myriadrf/STREAM/hardware/STREAM/v2/v2r1/KiCAD/Board power supply 1.sch

## KiCad design hardware/STREAM/v2/v2r1/KiCAD/Board power supply 1.sch (2015-03-17)

Schematic: Board power supply 1.sch

Parts:
C140, C155: 10UF_1206; SMD1206; Manufacturer Part Number CC1206ZKY5V7BB106
C141, C156: 22NF_0402; SMD0402; Manufacturer Part Number CC0402KRX7R9BB103
C142, C157: 2.2NF_0402; SMD0402; Manufacturer Part Number CL05B222KB5NNNC
C143, C160: 22PF_0402; SMD0402; Manufacturer Part Number CC0402JRNPO9BN220
C144, C161: 0.33UF_0603; SMD0603; Manufacturer Part Number MCCA000526
C145, C162: 22UF_0805; SMD0805; Manufacturer Part Number C2012X5R0J226M125AC
C151: 1UF_0402; C_SM0402; Manufacturer Part Number CC0402ZRY5V5BB105
C152, C158, C163: 10UF_0805; C_SM0805; Manufacturer Part Number C2012JB0J106K125AB
C154: 100NF_0402; C_SM0402; Manufacturer Part Number C0402C104K8PACTU
C164: 220UF_AL_CAP; 6.3mm_Al_cap; Manufacturer Part Number UCD1C221MCL1GS
C166: 10UF_0805; C_SM0402; Manufacturer Part Number C2012JB0J106K125AB
C176, C178: 2.2UF_0603; C_SM0603; Manufacturer Part Number CC0603ZRY5V6BB225
C181: 47UF_1206; C_SM1206; Manufacturer Part Number GRM31CR60J476ME19L
D1, D10: 20BQ030; SMB; Manufacturer Part Number VS-20BQ030TRPBF
D2, D12: TS4148; SM0805; Manufacturer Part Number TS4148 RY
IC16: TPS51100DGQ; 10MSOP; Manufacturer Part Number TPS51100DGQ
IC18: MIC37122Y_ADJ; SOIC8; Manufacturer Part Number MIC37122YM TR
IC24: NCP59151-ADJ; D2PAK-5; Manufacturer Part Number NCP59151DS50R4G
J18: PWR_JACK__FC681495; PWR_JACK_TH; Manufacturer Part Number FC681495
L2, L3: 22UH_XAL60XX_SERIES; XAL60xx series; Manufacturer Part Number XAL6060-223MEB
LD7, LD8: LED_0603_GREEN; LD_0603; Manufacturer Part Number HSMG-C190
R5, R156: 1K_0402; R_SM0402; Manufacturer Part Number RMCF0402FT1K00
R49, R130: 15K8_0402; SMD0402; Manufacturer Part Number CRCW040215K8FKED
R50, R131: 28K_0402; SMD0402; Manufacturer Part Number RC0402FR-0728KL
R51: 24K9_0402; SMD0402; Manufacturer Part Number RC1005F2492CS
R52, R144: 5K49_0402; SMD0402; Manufacturer Part Number RC0402FR-075K49L
R70: 2K32_0402; R_SM0402; Manufacturer Part Number RMCF0402FT2K32
R113: 0R_0402; R_SM0402; Manufacturer Part Number RC0402JR-070RL
R132: 22K1_0402; SMD0402; Manufacturer Part Number RC0402FR-0722K1L
R141, R142: 10K_0402; R_SM0402; Manufacturer Part Number RC0402FR-0710KL
R145, R160: 0R_0805; SM0805; Manufacturer Part Number ERJ-6GEY0R00V
R157: 470R_0402; R_SM0402; Manufacturer Part Number ERA-2AED471X
R158: 3K_0402; R_SM0402; Manufacturer Part Number CRCW04023K00FKED
R159: 750R_0402; R_SM0402; Manufacturer Part Number CRCW0402750RFKED
SW5: SW_ON-OFF; Switch_On_Off; Manufacturer Part Number L102021ML04Q
U3, U7: SC4524; SOIC-8; Manufacturer Part Number SC4524CSETRT

Notes on the sheet:
12V
EXTERNAL POWER SUPPLY
0.9V VTT (3A Sink/Src)
MyriadRF Power Supply
LTC4365CTS8#TRMPBFCT-ND
