myriadrf/STREAM/hardware/STREAM/v2/v2r1/KiCAD/Board power supply 2.sch

## KiCad design hardware/STREAM/v2/v2r1/KiCAD/Board power supply 2.sch (2015-03-17)

Schematic: Board power supply 2.sch

Parts:
C146, C147, C148, C149, C150, C177, C259: 2.2UF_0603; C_SM0603; Manufacturer Part Number CC0603ZRY5V6BB225
C182, C218: 100UF_1206; C_SM1206; Manufacturer Part Number GRM31CR60J107ME39L
C183: 15PF_0402; C_SM0402; Manufacturer Part Number CL05C150JB5NNNC
C184: 10PF_0402; SMD0402; Manufacturer Part Number CC0402JRNPO9BN100
C188, C189: 22UF_1206_X5R; C_SM1206; Manufacturer Part Number GRM31CR61C226ME15L
C190, C193: 47NF_0402; C_SM0402; Manufacturer Part Number GCM155R71C473KA37D
C191, C194, C200: 1UF_0402; C_SM0402; Manufacturer Part Number GRM155R61A105KE15J
C192: 0.22UF_0402; C_SM0402; Manufacturer Part Number C1005X5R1E224K050BC
C199, C205, C206, C207: 22UF_0805; C_SM0805; Manufacturer Part Number LMK212BJ226MG-T
C201, C202: 47UF_1206; C_SM1206; Manufacturer Part Number GRM31CR60J476ME19L
C301: 4.7UF_0805; C_SM0805; Manufacturer Part Number GRM219R60J475KE19D
IC14, IC19, IC20, IC21: MIC37122Y_ADJ; SOIC8; Manufacturer Part Number MIC37122YM TR
IC22: EN2390_2PARTS; 76QFN; Manufacturer Part Number EN2390QI
IC23: EN5339QI; 24QFN; Manufacturer Part Number EN5339QI
LD6: LED_0603_GREEN; LD_0603; Manufacturer Part Number HSMG-C190
R99: 100R_0402_1%; R_SM0402; Manufacturer Part Number RC0402FR-07100RL
R133, R134, R153: 1K_0402; R_SM0402; Manufacturer Part Number RMCF0402FT1K00
R135, R154: 806R_0402; R_SM0402; Manufacturer Part Number ERA-2AEB8060X
R136: 1K5_0402; R_SM0402; Manufacturer Part Number RC0402JR-071K5L
R137, R139, R155, R281: 0R_0402; R_SM0402; Manufacturer Part Number RC0402JR-070RL
R140: 470R_0402; R_SM0402; Manufacturer Part Number ERA-2AED471X
R164, R166: 10K_0402; R_SM0402; Manufacturer Part Number RC0402FR-0710KL
R165: 2K4_0402; R_SM0402; Manufacturer Part Number RC0402JR-072K4L
R168, R171, R179: 100K_0402; R_SM0402; Manufacturer Part Number RC0402JR-07100KL
R169: 4K75_0402; R_SM0402; Manufacturer Part Number RC0402FR-074K75L
R170: 15K_0402; R_SM0402; Manufacturer Part Number RC0402FR-0715KL
R175: 75K_0402; R_SM0402; Manufacturer Part Number RMCF0402FT75K0
R176: 5K1_0402; R_SM0402; Manufacturer Part Number RC0402FR-075K1L
R177: 16K5_0402; R_SM0402; Manufacturer Part Number 5-1879215-5
R180, R181: 348K_0402; R_SM0402; Manufacturer Part Number RC1005F3483CS
R280: 200R/1%_0402; R_SM0402; Manufacturer Part Number RC0402FR-07200RL
R282: 33K_0402; R_SM0402; Manufacturer Part Number MCR01MRTF3302

Notes on the sheet:
(+3.3V / 9A)
