myriadrf/STREAM/hardware/STREAM/v2/v2r1/KiCAD/Clocks.sch

## KiCad design hardware/STREAM/v2/v2r1/KiCAD/Clocks.sch (2015-03-17)

Schematic: Clocks.sch

Parts:
C93, C99: 100NF_0402; C_SM0402; Manufacturer Part Number C0402C104K8PACTU
C94, C95, C96: 22PF_0402; SMD0402; Manufacturer Part Number CC0402JRNPO9BN220
C97, C98, C307: 100NF_0402; SMD0402; Manufacturer Part Number CC0402ZRY5V7BB104
C100, C101, C102, C103, C105, C106, C107, C108, C109, C110: 100PF_0402; C_SM0402; Manufacturer Part Number CC0402JRNPO9BN101
C219, C316: 7PF_0402_NF; C_SM0402; Manufacturer Part Number C1005CH1H070C050BA
C308: 10PF_0402; SMD0402; Manufacturer Part Number CC0402JRNPO9BN100
C309, C311: 10NF_0402; SMD0402; Manufacturer Part Number CC0402KRX7R9BB103
C310: 220PF_0402; SMD0402; Manufacturer Part Number CC0402KRX7R9BB221
FB1: FB_600R_0402; SM0402; Manufacturer Part Number MMZ1005S601C
IC11: SI5351C; QFN20; Manufacturer Part Number SI5351C-B-GM
IC12: LMK00105; 24LLP; Manufacturer Part Number LMK00105SQ/NOPB
LD5: LED; LED_0603; Manufacturer Part Number LG Q971-KN-1
R111, R117: 470R_0402; SMD0402; Manufacturer Part Number ERA-2AED471X
R112: 330R_0402; SMD0402; Manufacturer Part Number RC0402JR-07330RL
R116: 10R_0402; SMD0402; Manufacturer Part Number RC0402JR-0710RL
R118, R150, R278: 0R_0402; R_SM0402; Manufacturer Part Number RC0402JR-070RL
R119, R125, R127, R151, R277: 0R_0402_NF; R_SM0402; Manufacturer Part Number RC0402JR-070RL
R120: 1K_0402; SMD0402; Manufacturer Part Number RMCF0402FT1K00
R121: 10K_0402; R_SM0402; Manufacturer Part Number RC0402FR-0710KL
R122, R123, R124: 47R_0402; SMD0402; Manufacturer Part Number RC0402FR-0747RL
U2: ADF4002; LFCSP 20; Manufacturer Part Number ADF4002BCPZ-RL7
X1: U.FL; Manufacturer Part Number 0734120110
XO4: TCXO_25MHZ_ABM8; 4-SMD; Manufacturer Part Number ABM8-25.000MHZ-B2-T
XO5: RACON_TXCO_PLUTO+; SMD_TXCO_Pluto+; Manufacturer Part Number E6245LF
