myriadrf/STREAM/hardware/STREAM/v2/v2r1/KiCAD/ClocksEVB.sch

## KiCad design hardware/STREAM/v2/v2r1/KiCAD/ClocksEVB.sch (2015-03-17)

Schematic: ClocksEVB.sch

Parts:
C120, C122, C123, C124, C125, C126, C128, C129, C131, C132, C133, C165, C167, C168: 100NF_0402; SMD0402; Manufacturer Part Number CC0402ZRY5V7BB104
C134, C135: 10NF_0402; SMD0402; Manufacturer Part Number CC0402KRX7R9BB103
C136: 220PF_0402; SMD0402; Manufacturer Part Number CC0402KRX7R9BB221
C137, C138, C139: 22PF_0402; SMD0402; Manufacturer Part Number CC0402JRNPO9BN220
C169, C170, C171, C172, C173, C174: 100PF_0402; SMD0402; Manufacturer Part Number CC0402JRNPO9BN101
C205: 10PF_0402; SMD0402; Manufacturer Part Number CC0402JRNPO9BN100
FB19: FB_600R_0402; SM0402; Manufacturer Part Number MMZ1005S601C
LD2: LED; LED_0603; Manufacturer Part Number LG Q971-KN-1
R10, R73, R104, R105, R136: 0R_0402; SMD0402; Manufacturer Part Number RC0402JR-070RL
R11, R74, R76, R137, R138, R144, R168, R173: 0R_0402_NF; SMD0402; Manufacturer Part Number RC0402JR-070RL
R39, R46, R59, R140: 47R_0402; SMD0402; Manufacturer Part Number RC0402FR-0747RL
R75: 2K2_0402; SMD0402; Manufacturer Part Number RC0402FR-072K2L
R77, R79, R81: 1K_0402; SMD0402; Manufacturer Part Number RMCF0402FT1K00
R80: 10R_0402; SMD0402; Manufacturer Part Number RC0402JR-0710RL
R82, R83: 470R_0402; SMD0402; Manufacturer Part Number ERA-2AED471X
R84: 10K_0402; SMD0402; Manufacturer Part Number RMCF0402FT10K0
R85: 330R_0402; SMD0402; Manufacturer Part Number RC0402JR-07330RL
U10: NC7SV74; US8; Manufacturer Part Number NC7SV74K8X
U11: SI5351C; QFN20; Manufacturer Part Number SI5351C-B-GM
U12, U13: SN74LVC1G04DBVR; SOT23-5; Manufacturer Part Number SN74LVC1G04DBVR
U15: ADF4002; LFCSP 20; Manufacturer Part Number ADF4002BCPZ-RL7
U24: LMK00105; 24LLP; Manufacturer Part Number LMK00105SQ/NOPB
X18: SMA_VERT_SMD; SMA_vert_SMD; Manufacturer Part Number 0732511352
X52: U.FL; Manufacturer Part Number 0734120110
XO1: TCXO_30.72MHZ; Manufacturer Part Number E5280LF
XO2: TCXO_61.44MHZ; TCXO CFPT-6144MHz; Manufacturer Part Number E5405LF
XO3: RACON_TXCO_PLUTO+; SMD_TXCO_Pluto+; Manufacturer Part Number E6245LF
