myriadrf/STREAM/hardware/STREAM/v2/v2r1/KiCAD/Connector.sch

## KiCad design hardware/STREAM/v2/v2r1/KiCAD/Connector.sch (2015-03-17)

Schematic: Connector.sch

Parts:
C140: 0.33UF_0603; SMD0603; Manufacturer Part Number MCCA000526
C141: 10UF_1206; SMD1206; Manufacturer Part Number CC1206ZKY5V7BB106
C142: 22NF_0402; SMD0402; Manufacturer Part Number CC0402KRX7R9BB103
C143: 22UF_0805; SMD0805; Manufacturer Part Number C2012X5R0J226M125AC
C144: 22PF_0402; SMD0402; Manufacturer Part Number CC0402JRNPO9BN220
C145: 2.2NF_0402; SMD0402; Manufacturer Part Number CL05B222KB5NNNC
D1: TS4148; SM0805; Manufacturer Part Number TS4148 RY
D2: 20BQ030; SMB; Manufacturer Part Number VS-20BQ030TRPBF
J6: FMC; Manufacturer Part Number ASP-134604-01
J7: PINHEADER2X22; Manufacturer Part Number 6739810180440
JP2: PINHEADER_2X2; Manufacturer Part Number 0015912040
L37: 22UH_XAL60XX_SERIES; XAL60xx series; Manufacturer Part Number XAL6060-223MEB
R45, R87: 10K_0402_NF; SMD0402; Manufacturer Part Number RMCF0402FT10K0
R47, R88: 10K_0402; SMD0402; Manufacturer Part Number RMCF0402FT10K0
R86, R89, R97: 0R_0402; SMD0402; Manufacturer Part Number RC0402JR-070RL
R91, R92, R93, R94, R95, R96: 0R_0402_NF; SMD0402; Manufacturer Part Number RC0402JR-070RL
R98: 22K1_0402; SMD0402; Manufacturer Part Number RC0402FR-0722K1L
R99: 15K8_0402; SMD0402; Manufacturer Part Number CRCW040215K8FKED
R100: 28K_0402; SMD0402; Manufacturer Part Number RC0402FR-0728KL
R101: 5K49_0402; SMD0402; Manufacturer Part Number RC0402FR-075K49L
U16: SC4524; SOIC-8; Manufacturer Part Number SC4524CSETRT
