myriadrf/STREAM/hardware/STREAM/v2/v2r1/KiCAD/Ethernet.sch

## KiCad design hardware/STREAM/v2/v2r1/KiCAD/Ethernet.sch (2015-03-17)

Schematic: Ethernet.sch

Parts:
C76, C82, C83, C84, C85, C86, C87, C88, C89, C90, C91, C92, C104, C175, C179, C180, C313, C314, C315: 100NF_0402; C_SM0402; Manufacturer Part Number C0402C104K8PACTU
C79: 10UF_0603; C_SM0603; Manufacturer Part Number CC0603MRX5R5BB106
C80, C81: 7PF_0402; C_SM0402; Manufacturer Part Number C1005CH1H070C050BA
FR8, FR10, FR12: FR_600R_0402; R_SM0402; Manufacturer Part Number MMZ1005S601C
IC10: KSZ9021GN; QFN64; Manufacturer Part Number LAN8720A-CP-TR
J9: RJ45_L829-1J1T-43; Manufacturer Part Number L829-1J1T-43
R75, R94: 10K_0402; R_SM0402; Manufacturer Part Number RC0402FR-0710KL
R76, R77: 4K7_0402; R_SM0603; Manufacturer Part Number RC0402JR-074K7L
R82: 4K99_0603; R_SM0603; Manufacturer Part Number RC0603FR-074K99L
R83: 220R_0402; R_SM0402; Manufacturer Part Number RC0402JR-07220RL
R84, R86, R90, R92, R96, R100, R106, R108: 10K_0402_NF; R_SM0402; Manufacturer Part Number RC0402FR-0710KL
R87, R91, R93, R97, R101, R107, R109, R110: 1K_0402; R_SM0402; Manufacturer Part Number RMCF0402FT1K00
R95: 1K_0402_NF; R_SM0402; Manufacturer Part Number RMCF0402FT1K00
R128: 22R_0402; R_SM0402; Manufacturer Part Number RC0402FR-0722RL
SW3: SW_TACTILE; SW_B3U-1000P; Manufacturer Part Number B3U-1000P
XO3: TCXO_25MHZ_ABM8; 4-SMD; Manufacturer Part Number ABM8-25.000MHZ-B2-T

Notes on the sheet:
MODE3
MODE2
MODE1
MODE0
Strapping Pins for MODE Selection
MODE[3:0] 0000 0001 0010-0011 0100 0101-0110 0111 1000-1111
Description reserved GMII / MII mode reserved NAND Tree mode reserved Chip Power Down reserved
PHYAD2
LED_MODE
CLK125_EN
PHYAD1
PHYAD0
Strapping Pins for LED Mode
Strapping Pins for CLK125 Enable
Strapping Pins for PHY Address
Pins [LED2, LED1] [0, 1] [toggling, 1] [1, 0] [1, toggling] [0, 0] [toggling, toggling] [1, 1]
Description Solid Color : 1G Link Blinking : Activity (RX, TX) Solid Color : 100M Link Blinking : Activity (RX, TX) Solid Color : 10M Link Blinking : Activity (RX, TX) Link off
Dual LED Color Green Red Orange None
Tri-color Dual LED Mode
