myriadrf/STREAM/hardware/STREAM/v2/v2r1/KiCAD/Board block diagram.sch

## KiCad design hardware/STREAM/v2/v2r1/KiCAD/FMC and Myriad RF connectors.sch

Schematic: FMC  and Myriad RF connectors.sch

Parts:
J20: FX10B_80S_8; Manufacturer Part Number FX10B-80S/8-SV(71)
J21: FMC_FEMALE_LOW_COUNT; FMC_Female; Manufacturer Part Number ASP-134603-01
J22: PINHEADER_1X2_TH; Pinhead_1x2_TH; Manufacturer Part Number 5-146285-2
R146, R189, R190, R191, R192, R193, R194, R199: 0R_0402_NF; R_SM0402; Manufacturer Part Number RC0402JR-070RL
R163, R167: 4K7_0402; R_SM0402; Manufacturer Part Number RC0402JR-074K7L
R195, R197: 10K_0402_NF; R_SM0402; Manufacturer Part Number RC0402FR-0710KL
R196, R198: 10K_0402; R_SM0402; Manufacturer Part Number RC0402FR-0710KL

Notes on the sheet:
TX DAC
RX ADC
Myriad RF Connector
FMC Connector
