myriadrf/STREAM/hardware/STREAM/v2/v2r1/KiCAD/FPGA banks 1_4.sch

## KiCad design hardware/STREAM/v2/v2r1/KiCAD/FPGA banks 1_4.sch (2015-03-17)

Schematic: FPGA banks 1_4.sch

Parts:
C32, C33, C35, C36, C174, C185, C288, C289: 100NF_0201; SM0402; Manufacturer Part Number GRM033R60J104KE19D
C304: 100NF_0402; C_SM0402; Manufacturer Part Number C0402C104K8PACTU
IC1: EP4CE40F23C7N; LMS_SyntCLK1; Manufacturer Part Number EP4CE40F23C7N
J23: PINHEADER_2X5_TH_WALL; Pinhead_2x6_TH_WALL; Manufacturer Part Number SBH11-PBPC-D05-ST-BK
LD9, LD10: LED_0603_GREEN; LD_0603; Manufacturer Part Number HSMG-C190
R85, R88, R89, R98, R200, R202: 10K_0402; R_SM0402; Manufacturer Part Number RC0402FR-0710KL
R102, R103: 22R_0402; R_SM0402; Manufacturer Part Number RC0402FR-0722RL
R201: 1K_0402; R_SM0402; Manufacturer Part Number RMCF0402FT1K00
R203: 100K_0402; R_SM0402; Manufacturer Part Number RC0402JR-07100KL
SW1: SW_DIP_4POLES; SW_DIP_4poles; Manufacturer Part Number A6H-4101
SW4: SW_TACTILE; SW_B3U-1000P; Manufacturer Part Number B3U-1000P
TP4, TP5: TP

Notes on the sheet:
Bank3
Bank4
FPGA JTAG
FPGA reset circuit
ON = "0" OFF = "1"
FPGA_LED0
FPGA_LED1
