myriadrf/STREAM/hardware/STREAM/v2/v2r1/KiCAD/FPGA banks 5_8.sch

## KiCad design hardware/STREAM/v2/v2r1/KiCAD/FPGA banks 5_8.sch (2015-03-17)

Schematic: FPGA banks 5_8.sch

Parts:
IC1: EP4CE40F23C7N; 484FBGA; Manufacturer Part Number EP4CE40F23C7N
J1: PINHEADER_2X5_TH_WALL; Pinhead_2x6_TH_WALL; Manufacturer Part Number SBH11-PBPC-D05-ST-BK
LD11: LED_0603_GREEN; LD_0603; Manufacturer Part Number HSMG-C190
R1, R2, R3, R4: 0R_0402_NF; R_SM0402; Manufacturer Part Number RC0402JR-070RL
R78, R147: 10K_0402; R_SM0402; Manufacturer Part Number RC0402FR-0710KL
R79, R80, R81, R114, R161, R162, R279: 0R_0402; R_SM0402; Manufacturer Part Number RC0402JR-070RL
R300: 22R_0402; R_SM0402; Manufacturer Part Number RC0402FR-0722RL
TP2: TP

Notes on the sheet:
MSEL[3:0] Configuration
Passive Serial Standard (MSEL[3:0]=0000)
FPGA_LED2
