myriadrf/STREAM/hardware/STREAM/v2/v2r1/KiCAD/FPGA power distribution.sch

## KiCad design hardware/STREAM/v2/v2r1/KiCAD/FPGA power distribution.sch (2015-03-17)

Schematic: FPGA power distribution.sch

Parts:
C187, C220, C223, C226, C229, C235, C244: 10NF_0402; C_SM0402; Manufacturer Part Number CC0402KRX7R9BB103
C210, C296, C298, C299, C300, C303: 4.7UF_0805; C_SM0805; Manufacturer Part Number GRM219R60J475KE19D
C211, C214, C216, C217: 100UF_1206; C_SM1206; Manufacturer Part Number GRM31CR60J107ME39L
C221, C224, C227, C230, C239, C249: 100NF_0402; C_SM0402; Manufacturer Part Number C0402C104K8PACTU
C222, C225, C228, C231, C240, C254: 1UF_0402; C_SM0402; Manufacturer Part Number GRM155R61A105KE15J
C232, C233, C234, C236, C237, C238, C241, C242, C243, C245, C246, C247, C248, C250, C251, C252, C253, C255, C256, C257, C258, C260, C261, C262, C263, C266, C267, C268, C270, C271, C272, C273, C274, C275, C276, C277, C279, C280, C284, C285, C290, C291, C292, C293: 100NF_0201; SM0402; Manufacturer Part Number GRM033R60J104KE19D
FR21: FR_600R_0402; R_SM0402; Manufacturer Part Number MMZ1005S601C
IC1: EP4CE40F23C7N; 484FBGA; Manufacturer Part Number EP4CE40F23C7N

Notes on the sheet:
Bank1
Bank2
Bank3
Bank8
Bank4
Bank5
Bank6
Bank7
VCCD_PLL
VCCINT
VCCA
