myriadrf/STREAM/hardware/STREAM/v2/v2r1/KiCAD/Peripherals.sch

## KiCad design hardware/STREAM/v2/v2r1/KiCAD/Peripherals.sch (2015-03-17)

Schematic: Peripherals.sch

Parts:
C57: 1UF_0402; C_SM0402; Manufacturer Part Number CC0402ZRY5V5BB105
C69, C70, C71, C74, C75, C77, C78, C171, C173, C203, C204: 100NF_0402; C_SM0402; Manufacturer Part Number C0402C104K8PACTU
C72: 10UF_0603; C_SM0603; Manufacturer Part Number CC0603MRX5R5BB106
C73, C169, C170, C198: 1UF_0402; C_SM0402; Manufacturer Part Number GRM155R61A105KE15J
C197: 100UF_1206; C_SM1206; Manufacturer Part Number GRM31CR60J107ME39L
D7: MMSZ5222BT1G; SOD-123; Manufacturer Part Number MMSZ5222BT1G
IC9: TFP410; 64-TQFP; Manufacturer Part Number TFP410MPAPREP
J8: PINHEADER_2X2; Manufacturer Part Number 0015912040
J12: HDMI; HDMI_Conn; Manufacturer Part Number 10029449-111RLF
J13: AMP_MICTOR38; AMP_Mictor38; Manufacturer Part Number 2-5767004-2
Q1: BSS138PS; SOT-363; Manufacturer Part Number BSS138PS,115
R58, R208, R269, R275: 0R_0402; R_SM0402; Manufacturer Part Number RC0402JR-070RL
R65: 510R_0603; R_SM0603; Manufacturer Part Number RC0603FR-07510RL
R66, R68, R69, R148, R149, R267: 10K_0402; R_SM0402; Manufacturer Part Number RC0402FR-0710KL
R67, R143: 51R_0402; SMD0402; Manufacturer Part Number RC0402JR-0751RL
R72, R271: 4K7_0402; R_SM0603; Manufacturer Part Number RC0402JR-074K7L
R266, R268, R272, R273, R274, R276: 0R_0402_NF; R_SM0402; Manufacturer Part Number RC0402JR-070RL
R270: 3K9_0402; R_SM0402; Manufacturer Part Number ERJ-2RKF3901X
U6: NCP380HSN05AAT1G; 5-TSOP; Manufacturer Part Number NCP380HSN05AAT1G
U8: LP5900SD-3.3; SC70; Manufacturer Part Number LP5900SD-3.3/NOPB
U9, U10: ADCS7476AIMF; SOT-23-6; Manufacturer Part Number ADCS7476AIMF/NOPB

Notes on the sheet:
Mictor 38
(5V / 0.5A)
