myriadrf/STREAM/hardware/STREAM/v2/v2r1/KiCAD/SDRAM.sch

## KiCad design hardware/STREAM/v2/v2r1/KiCAD/SDRAM.sch (2015-03-17)

Schematic: SDRAM.sch

Parts:
C1, C2, C3, C4, C5, C6, C7, C8, C9, C10, C11, C12, C13, C14, C15, C16, C17, C18, C19, C20, C21, C22, C23, C24, C25, C26, C27, C28, C29, C30, C31, C34, C37, C38, C39, C40, C186, C195, C196: 100NF_0402; C_SM0402; Manufacturer Part Number C0402C104K8PACTU
IC2, IC3: W9751G6KB-25; 84WBGA; Manufacturer Part Number W9751G6KB-25
R6, R7, R8, R9, R10, R11, R13, R14, R15, R16, R17, R18, R71, R126, R138, R152, R172, R173, R174, R178, R182, R183, R184, R185, R186, R187, R188, R209, R210, R211, R212, R213, R214, R215, R216, R217, R218, R219, R220, R221, R222, R223, R224, R225, R226, R227, R228, R229, R230, R231, R232, R233, R234, R235, R236, R237, R238, R239, R240, R241, R242, R243, R244, R245, R246, R247, R248, R249, R250, R251, R252, R253, R254, R255, R256, R257, R258, R259, R260, R261, R262, R263: 56R_0201; SMD0201; Manufacturer Part Number RC0603F560CS
