myriadrf/STREAM/hardware/STREAM/v2/v2r1/KiCAD/Stream.sch

## KiCad design hardware/STREAM/v2/v2r1/KiCAD/Stream.sch (2015-03-17)

Schematic: Stream.sch

Parts:
FD1, FD2, FD3, FD4, FD5, FD6: FIDUCIAL; Fiducial
MH1, MH2, MH3, MH4: MOUNTHOLLE; MH

Notes on the sheet:
12V Power supply chain (VCC12) 5V Power supply chain (VCC5)
3.3V Power supply chain (VCC3P3)
FPGA BANKS 1-4
FPGA BANKS 5-8
BOARD BLOCK DIAGRAM
CLOCKS BLOCK DIAGRAM
SDRAM
FMC & MYRIAD RF CONNECTORS
USB 3.0 Device (FX3)
USB 2.0 Host
PERIPHERRALS
ETHERNET
CLOCKS
FPGA POWER DISTRIBUTION
USB 3.0 POWER SUPPLY
BOARD POWER SUPPLY 1
BOARD POWER SUPPLY 2
Page 2
Page 14
Page 17
Page 4
Page 5
Page 16
Page 6
Page 7
Page 13
Page 15
Page 10
Page 8
Page 12
Page 11
Page 9
DVI HDMI connector Mictor38 (Agilent) connenctor
Including: FX3 Memory FX3 JTAG
