myriadrf/STREAM/hardware/STREAM/v2/v2r1/KiCAD/USB 2.0 Host.sch

## KiCad design hardware/STREAM/v2/v2r1/KiCAD/USB 2.0 Host.sch (2015-03-17)

Schematic: USB 2.0 Host.sch

Parts:
C49, C55: 1UF_0402; C_SM0402; Manufacturer Part Number GRM155R61A105KE15J
C50, C52: 100UF_1206; C_SM1206; Manufacturer Part Number GRM31CR60J107ME39L
C51, C53, C54, C56: 47PF_0402; C_SM0402; Manufacturer Part Number CC0402JRNPO9BN470
C59: 1UF_0603; C_SM0603; Manufacturer Part Number CC0603ZRY5V7BB105
C60, C61: 10PF_0402; SMD0402; Manufacturer Part Number CC0402JRNPO9BN100
C62: 10UF_0603; C_SM0603; Manufacturer Part Number CC0603MRX5R5BB106
C63, C64, C66, C67, C68: 100NF_0402; C_SM0402; Manufacturer Part Number C0402C104K8PACTU
C65: 22UF_0805; C_SM0805; Manufacturer Part Number C2012X5R0J226M125AC
D6: PMEG2010AEB_NF; SC-79; Manufacturer Part Number PMEG2010AEB,115
IC7: SRV05-4; SOT-23-6; Manufacturer Part Number SRV05-4HTG
IC8: VNC2-48L1B; 48-LQFP; Manufacturer Part Number VNC2-48L1B-REEL
J6, J7: USB2_A; TH-USB2_A; Manufacturer Part Number A-USB/2-A-E-R
J10: USD; MicroSD; Manufacturer Part Number 114-00841-68
J11: PINHEADER_1X6_2MM_TH_RIGHT; Pinhead_1x6_2mm_TH_right; Manufacturer Part Number M22-2530605
L1: 470NH_0603; L_SM0603; Manufacturer Part Number 0603AF-271XJRU
LD12, LD13: LED_0603_GREEN; LD_0603; Manufacturer Part Number HSMG-C190
R59, R60, R61, R62: 22R_0402; R_SM0402; Manufacturer Part Number RC0402FR-0722RL
R63, R64: 470R_0402; R_SM0402; Manufacturer Part Number ERA-2AED471X
R129, R264, R265: 10K_0402; R_SM0402; Manufacturer Part Number RC0402FR-0710KL
U4, U5: NCP380HSN05AAT1G; 5-TSOP; Manufacturer Part Number NCP380HSN05AAT1G
XO2: TCXO_12MHZ_7M; 4-SMD; Manufacturer Part Number 7M-12.000MEEQ-T

Notes on the sheet:
(5V / 0.5A)
uSD (External Memory)
