myriadrf/STREAM/hardware/STREAM/v2/v2r1/KiCAD/USB 3.0 Device (FX3).sch

## KiCad design hardware/STREAM/v2/v2r1/KiCAD/USB 3.0 Device (FX3).sch (2015-03-17)

Schematic: USB 3.0 Device (FX3).sch

Parts:
C41, C44, C45, C46, C47, C48, C305: 100NF_0402; C_SM0402; Manufacturer Part Number C0402C104K8PACTU
C42, C43: 13PF_0402; C_SM0402; Manufacturer Part Number GRM1555C1H130JA01D
C153, C208, C209: 1UF_0402; C_SM0402; Manufacturer Part Number GRM155R61A105KE15J
C306: 10UF_0603; C_SM0603; Manufacturer Part Number CC0603MRX5R5BB106
FR1, FR2: FR_220R_0402; R_SM0402; Manufacturer Part Number MPZ1005S221E
IC4: SP3010-04UTG; uDFN-10; Manufacturer Part Number SP3010-04UTG
IC5: M25P40; SOIC-8; Manufacturer Part Number M25P40-VMN6TPB
IC6: CYUSB3013; 121TFBGA; Manufacturer Part Number CYUSB3013-BZXC
IC13: SN74AVC2T245; 10UQFN; Manufacturer Part Number SN74AVC2T245RSWR
IC15: M25P16; SOIC-8; Manufacturer Part Number M25P16-VMN6TP
J2: USB3_MICROB_SMD; USB3_microB_SMD; Manufacturer Part Number 690-010-295-484
J3: PINHEADER_1X2_SMD; PINHEADER_1x2_SMD; Manufacturer Part Number M20-8770246
J4: PINHEADER_2X8_SMD_RA; Manufacturer Part Number 961216-5500-AR-PR
J5: JTAG_PIN_2X10_SMD_WALL; Pinhead_2x10_SMD_wall; Manufacturer Part Number SBH11-NBPC-D10-SM-BK
LD1, LD2, LD3: LED_0603_YELLOW; LD_0603; Manufacturer Part Number LTST-C194KSKT
LD4: LED_0603_GREEN; LD_0603; Manufacturer Part Number HSMG-C190
Q2: BSS138PS; SOT-363; Manufacturer Part Number BSS138PS,115
R12: 750R_0402; R_SM0402; Manufacturer Part Number CRCW0402750RFKED
R19, R20, R21: 470R_0402; R_SM0402; Manufacturer Part Number ERA-2AED471X
R22, R104, R105: 0R_0402_NF; R_SM0402; Manufacturer Part Number RC0402JR-070RL
R23, R24, R25, R27, R28, R29: 4K7_0402; R_SM0603; Manufacturer Part Number RC0402JR-074K7L
R26, R43, R48: 100K_0402; R_SM0402; Manufacturer Part Number RC0402JR-07100KL
R30: 6.04K/1%_0402; R_SM0402; Manufacturer Part Number CRCW04026K04FKED
R31: 200R/1%_0402; R_SM0402; Manufacturer Part Number RC0402FR-07200RL
R32, R33, R34, R35, R36, R37, R44: 10K_0402; R_SM0402; Manufacturer Part Number RC0402FR-0710KL
R38, R39, R40, R41, R42, R46: 0R_0402; R_SM0402; Manufacturer Part Number RC0402JR-070RL
R45, R47: 10K_0402_NF; R_SM0402; Manufacturer Part Number RC0402FR-0710KL
R53, R54, R55, R204, R205, R206, R207: RA4_22R; R_array; Manufacturer Part Number YC124-JR-0722RL
R56, R57: 22R_0402; R_SM0402; Manufacturer Part Number RC0402FR-0722RL
R73, R74, R283, R284: 4K7_0402; R_SM0402; Manufacturer Part Number RC0402JR-074K7L
R115: 2K2_0402; SMD0402; Manufacturer Part Number RC0402FR-072K2L
SW2: SW_TACTILE; SW_B3U-1000P; Manufacturer Part Number B3U-1000P
TP1: TP
XO1: TCXO_19.2MHZ; 4-SMD; Manufacturer Part Number 405C35B19M20000

Notes on the sheet:
FX3 JTAG
FX3 MEMORY
FX3 LEDs
