myriadrf/STREAM/hardware/STREAM/v2/v2r1/KiCAD/USB 3.0 power supply.sch

## KiCad design hardware/STREAM/v2/v2r1/KiCAD/USB 3.0 power supply.sch (2015-03-17)

Schematic: USB 3.0 power supply.sch

Parts:
C58, C118, C127, C128, C129, C130, C132, C133, C135, C138, C139, C159, C165, C172: 10NF_0402; C_SM0402; Manufacturer Part Number CC0402KRX7R9BB103
C111, C112, C113, C114, C115, C117, C119, C120, C122, C123, C125, C126, C131, C134, C136, C137, C167, C168: 100NF_0402; C_SM0402; Manufacturer Part Number C0402C104K8PACTU
C116, C121, C124, C317, C318, C319, C320, C321: 22UF_0805; C_SM0805; Manufacturer Part Number LMK212BJ226MG-T
C212: 4.7UF_0805; C_SM0805; Manufacturer Part Number GRM219R60J475KE19D
FR13, FR14, FR15, FR16, FR17, FR18, FR19, FR20: FR_600R_0805_2A; R_SM0805; Manufacturer Part Number MPZ2012S601AT000
IC6: CYUSB3013; 121-TFBGA; Manufacturer Part Number CYUSB3013-BZXC

Notes on the sheet:
VIO1
VDD
VIO2
VIO3
VIO4
VIO5
