myriadrf/STREAM/apps/lms7_usb_distro_01v/gateware/qii_projects/uStream_mrf7_trx_restored/lms7_ustream_trx.qsf

# -------------------------------------------------------------------------- #
#
# Copyright (C) 1991-2014 Altera Corporation
# Your use of Altera Corporation's design tools, logic functions
# and other software and tools, and its AMPP partner logic
# functions, and any output files from any of the foregoing
# (including device programming or simulation files), and any
# associated documentation or information are expressly subject
# to the terms and conditions of the Altera Program License
# Subscription Agreement, Altera MegaCore Function License
# Agreement, or other applicable license agreement, including,
# without limitation, that your use is for the sole purpose of
# programming logic devices manufactured by Altera and sold by
# Altera or its authorized distributors.  Please refer to the
# applicable agreement for further details.
#
# -------------------------------------------------------------------------- #
#
# Quartus II 64-Bit
# Version 13.1.4 Build 182 03/12/2014 SJ Web Edition
# Date created = 15:33:18  May 22, 2015
#
# -------------------------------------------------------------------------- #
#
# Notes:
#
# 1) The default values for assignments are stored in the file:
#		lms7_ustream_trx_assignment_defaults.qdf
#    If this file doesn't exist, see file:
#		assignment_defaults.qdf
#
# 2) Altera recommends that you do not modify this file. This
#    file is updated automatically by the Quartus II software
#    and any changes you make may be lost or overwritten.
#
# -------------------------------------------------------------------------- #


set_global_assignment -name FAMILY "Cyclone IV E"
set_global_assignment -name DEVICE EP4CE10F17C8
set_global_assignment -name TOP_LEVEL_ENTITY lms7_uStream_trx_top
set_global_assignment -name ORIGINAL_QUARTUS_VERSION 15.0.2
set_global_assignment -name PROJECT_CREATION_TIME_DATE "11:20:28  OCTOBER 07, 2015"
set_global_assignment -name LAST_QUARTUS_VERSION 15.0.0
set_global_assignment -name PROJECT_OUTPUT_DIRECTORY output_files
set_global_assignment -name MIN_CORE_JUNCTION_TEMP 0
set_global_assignment -name MAX_CORE_JUNCTION_TEMP 85
set_global_assignment -name ERROR_CHECK_FREQUENCY_DIVISOR 1
set_global_assignment -name EDA_SIMULATION_TOOL "ModelSim-Altera (VHDL)"
set_global_assignment -name EDA_OUTPUT_DATA_FORMAT VHDL -section_id eda_simulation
set_global_assignment -name POWER_PRESET_COOLING_SOLUTION "23 MM HEAT SINK WITH 200 LFPM AIRFLOW"
set_global_assignment -name POWER_BOARD_THERMAL_MODEL "NONE (CONSERVATIVE)"
set_global_assignment -name STRATIX_DEVICE_IO_STANDARD "2.5 V"
set_location_assignment PIN_E1 -to clk
set_location_assignment PIN_E11 -to FPGA_LED0
set_location_assignment PIN_E10 -to FPGA_LED1
set_location_assignment PIN_C11 -to FPGA_LED2
set_global_assignment -name CYCLONEIII_CONFIGURATION_SCHEME "PASSIVE SERIAL"
set_global_assignment -name USE_CONFIGURATION_DEVICE OFF
set_global_assignment -name CRC_ERROR_OPEN_DRAIN OFF
set_global_assignment -name RESERVE_DATA1_AFTER_CONFIGURATION "USE AS REGULAR IO"
set_global_assignment -name RESERVE_FLASH_NCE_AFTER_CONFIGURATION "USE AS REGULAR IO"
set_global_assignment -name OUTPUT_IO_TIMING_NEAR_END_VMEAS "HALF VCCIO" -rise
set_global_assignment -name OUTPUT_IO_TIMING_NEAR_END_VMEAS "HALF VCCIO" -fall
set_global_assignment -name OUTPUT_IO_TIMING_FAR_END_VMEAS "HALF SIGNAL SWING" -rise
set_global_assignment -name OUTPUT_IO_TIMING_FAR_END_VMEAS "HALF SIGNAL SWING" -fall
set_global_assignment -name GENERATE_RBF_FILE ON
set_location_assignment PIN_F6 -to FX3_SPI_MISO
set_location_assignment PIN_F7 -to FX3_SPI_MOSI
set_location_assignment PIN_B7 -to FX3_SPI_SCK
set_location_assignment PIN_A2 -to FPGA_LMS_CS
set_location_assignment PIN_E6 -to FPGA_SPI_MISO
set_location_assignment PIN_A5 -to FPGA_SPI_MOSI
set_location_assignment PIN_E7 -to FPGA_SPI_SCK
set_location_assignment PIN_B5 -to FPGA_DAC_CS
set_location_assignment PIN_A4 -to FX3_FPGA_GPIO1
set_location_assignment PIN_F3 -to LMS_RESET
set_location_assignment PIN_D8 -to RPI_GPIO12_miso
set_location_assignment PIN_E8 -to RPI_GPIO16_cs
set_location_assignment PIN_F8 -to RPI_GPIO20_mosi
set_location_assignment PIN_F9 -to RPI_GPIO21_sclk
set_location_assignment PIN_G2 -to RXD[11]
set_location_assignment PIN_J2 -to RXD[10]
set_location_assignment PIN_C1 -to RXD[9]
set_location_assignment PIN_G1 -to RXD[8]
set_location_assignment PIN_B3 -to RXD[7]
set_location_assignment PIN_F1 -to RXD[6]
set_location_assignment PIN_E5 -to RXD[5]
set_location_assignment PIN_F2 -to RXD[4]
set_location_assignment PIN_B1 -to RXD[3]
set_location_assignment PIN_D3 -to RXD[2]
set_location_assignment PIN_B6 -to RXD[1]
set_location_assignment PIN_D4 -to RXD[0]
set_location_assignment PIN_C3 -to RXIQSEL
set_location_assignment PIN_J1 -to TXD[11]
set_location_assignment PIN_L4 -to TXD[10]
set_location_assignment PIN_N2 -to TXD[9]
set_location_assignment PIN_K6 -to TXD[8]
set_location_assignment PIN_R1 -to TXD[7]
set_location_assignment PIN_P2 -to TXD[6]
set_location_assignment PIN_L6 -to TXD[5]
set_location_assignment PIN_K5 -to TXD[4]
set_location_assignment PIN_K1 -to TXD[3]
set_location_assignment PIN_P1 -to TXD[2]
set_location_assignment PIN_L2 -to TXD[1]
set_location_assignment PIN_L1 -to TXD[0]
set_location_assignment PIN_J6 -to TXIQSEL
set_global_assignment -name ENABLE_OCT_DONE OFF
set_global_assignment -name ENABLE_CONFIGURATION_PINS OFF
set_global_assignment -name ENABLE_BOOT_SEL_PIN OFF
set_location_assignment PIN_D16 -to FX3_PCLK
set_location_assignment PIN_G11 -to FX3_DQ[15]
set_location_assignment PIN_N13 -to FX3_DQ[3]
set_location_assignment PIN_M12 -to FX3_DQ[10]
set_location_assignment PIN_L12 -to FX3_DQ[13]
set_location_assignment PIN_K12 -to FX3_DQ[7]
set_location_assignment PIN_P16 -to FX3_DQ[0]
set_location_assignment PIN_R16 -to FX3_DQ[1]
set_location_assignment PIN_K11 -to FX3_DQ[4]
set_location_assignment PIN_N16 -to FX3_DQ[8]
set_location_assignment PIN_N15 -to FX3_DQ[6]
set_location_assignment PIN_L13 -to FX3_DQ[12]
set_location_assignment PIN_L16 -to FX3_DQ[9]
set_location_assignment PIN_L15 -to FX3_DQ[11]
set_location_assignment PIN_J11 -to FX3_DQ[5]
set_location_assignment PIN_K16 -to FX3_DQ[14]
set_location_assignment PIN_A3 -to FX3_FPGA_GPIO3
set_location_assignment PIN_F16 -to FX3_DQ[2]
set_location_assignment PIN_B16 -to FX3_FLAGA
set_location_assignment PIN_F15 -to FX3_FLAGB
set_location_assignment PIN_J14 -to FX3_FLAGC
set_location_assignment PIN_G16 -to FX3_FLAGD
set_location_assignment PIN_G15 -to FX3_A[0]
set_location_assignment PIN_J13 -to FX3_A[1]
set_location_assignment PIN_J12 -to FX3_PKTENDn
set_location_assignment PIN_K15 -to FX3_SLCSn
set_location_assignment PIN_J15 -to FX3_SLWRn
set_location_assignment PIN_F13 -to FX3_SLOEn
set_location_assignment PIN_D15 -to FX3_SLRDn
set_global_assignment -name CYCLONEII_RESERVE_NCEO_AFTER_CONFIGURATION "USE AS REGULAR IO"
set_location_assignment PIN_R8 -to mem_odt[0]
set_location_assignment PIN_M11 -to mem_clk[0]
set_location_assignment PIN_N12 -to mem_clk_n[0]
set_location_assignment PIN_L10 -to mem_cs_n[0]
set_location_assignment PIN_T2 -to mem_cke[0]
set_location_assignment PIN_K10 -to mem_addr[0]
set_location_assignment PIN_T8 -to mem_addr[1]
set_location_assignment PIN_L9 -to mem_addr[2]
set_location_assignment PIN_T10 -to mem_addr[3]
set_location_assignment PIN_N3 -to mem_addr[4]
set_location_assignment PIN_T9 -to mem_addr[5]
set_location_assignment PIN_K9 -to mem_addr[6]
set_location_assignment PIN_T15 -to mem_addr[7]
set_location_assignment PIN_P14 -to mem_addr[8]
set_location_assignment PIN_T11 -to mem_addr[9]
set_location_assignment PIN_T6 -to mem_addr[10]
set_location_assignment PIN_R13 -to mem_addr[11]
set_location_assignment PIN_T14 -to mem_addr[12]
set_location_assignment PIN_T5 -to mem_ba[0]
set_location_assignment PIN_T3 -to mem_ba[1]
set_location_assignment PIN_L11 -to mem_cas_n
set_location_assignment PIN_M9 -to mem_ras_n
set_location_assignment PIN_R9 -to mem_we_n
set_location_assignment PIN_N6 -to mem_dq[0]
set_location_assignment PIN_R6 -to mem_dq[1]
set_location_assignment PIN_N5 -to mem_dq[2]
set_location_assignment PIN_R7 -to mem_dq[3]
set_location_assignment PIN_R5 -to mem_dq[4]
set_location_assignment PIN_L7 -to mem_dq[5]
set_location_assignment PIN_R3 -to mem_dq[6]
set_location_assignment PIN_L8 -to mem_dq[7]
set_location_assignment PIN_R11 -to mem_dq[8]
set_location_assignment PIN_R10 -to mem_dq[9]
set_location_assignment PIN_N8 -to mem_dq[10]
set_location_assignment PIN_R12 -to mem_dq[11]
set_location_assignment PIN_T12 -to mem_dq[12]
set_location_assignment PIN_N9 -to mem_dq[13]
set_location_assignment PIN_T13 -to mem_dq[14]
set_location_assignment PIN_P8 -to mem_dq[15]
set_location_assignment PIN_P3 -to mem_dm[0]
set_location_assignment PIN_M8 -to mem_dm[1]
set_location_assignment PIN_M7 -to mem_dqs[0]
set_location_assignment PIN_T7 -to mem_dqs[1]
set_location_assignment PIN_A6 -to FX3_FPGA_SNN
set_location_assignment PIN_E9 -to RPI_GPIO19
set_location_assignment PIN_F10 -to RPI_GPIO26
set_location_assignment PIN_D9 -to RPI_GPIO6
set_location_assignment PIN_F11 -to RPI_GPIO13
set_location_assignment PIN_B8 -to FX3_GPIO5
set_global_assignment -name ENABLE_SIGNALTAP OFF
set_global_assignment -name USE_SIGNALTAP_FILE signal_tap/pll_phase.stp
set_location_assignment PIN_A9 -to RPI_MISO
set_location_assignment PIN_B10 -to RPI_MOSI
set_location_assignment PIN_A8 -to RPI_SCLK
set_location_assignment PIN_D14 -to RPI_SDA1
set_location_assignment PIN_B13 -to RPI_GCLK
set_location_assignment PIN_D12 -to RPI_GEN0
set_location_assignment PIN_A11 -to RPI_GEN3
set_global_assignment -name DEVICE_MIGRATION_LIST "EP4CE10F17C8,EP4CE6F17C8"
set_location_assignment PIN_B11 -to RPI_GEN4
set_location_assignment PIN_D11 -to RPI_ID_SD
set_global_assignment -name PARTITION_NETLIST_TYPE SOURCE -section_id Top
set_global_assignment -name PARTITION_FITTER_PRESERVATION_LEVEL PLACEMENT_AND_ROUTING -section_id Top
set_global_assignment -name PARTITION_COLOR 16764057 -section_id Top
set_instance_assignment -name IO_STANDARD "3.3-V LVCMOS" -to clk
set_instance_assignment -name IO_STANDARD "3.3-V LVCMOS" -to FPGA_LED0
set_instance_assignment -name IO_STANDARD "3.3-V LVCMOS" -to FPGA_LED1
set_instance_assignment -name IO_STANDARD "3.3-V LVCMOS" -to FPGA_LED2
set_instance_assignment -name IO_STANDARD "3.3-V LVCMOS" -to FX3_SPI_MISO
set_instance_assignment -name IO_STANDARD "3.3-V LVCMOS" -to FX3_SPI_MOSI
set_instance_assignment -name IO_STANDARD "3.3-V LVCMOS" -to FX3_SPI_SCK
set_instance_assignment -name IO_STANDARD "3.3-V LVCMOS" -to FPGA_LMS_CS
set_instance_assignment -name IO_STANDARD "3.3-V LVCMOS" -to FPGA_SPI_MISO
set_instance_assignment -name IO_STANDARD "3.3-V LVCMOS" -to FPGA_SPI_MOSI
set_instance_assignment -name IO_STANDARD "3.3-V LVCMOS" -to FPGA_SPI_SCK
set_instance_assignment -name IO_STANDARD "3.3-V LVCMOS" -to FPGA_DAC_CS
set_instance_assignment -name IO_STANDARD "3.3-V LVCMOS" -to FX3_FPGA_GPIO1
set_instance_assignment -name IO_STANDARD "3.3-V LVCMOS" -to LMS_RESET
set_instance_assignment -name IO_STANDARD "3.3-V LVCMOS" -to RPI_GPIO12_miso
set_instance_assignment -name IO_STANDARD "3.3-V LVCMOS" -to RPI_GPIO16_cs
set_instance_assignment -name IO_STANDARD "3.3-V LVCMOS" -to RPI_GPIO20_mosi
set_instance_assignment -name IO_STANDARD "3.3-V LVCMOS" -to RPI_GPIO21_sclk
set_instance_assignment -name IO_STANDARD "3.3-V LVCMOS" -to RXD[11]
set_instance_assignment -name IO_STANDARD "3.3-V LVCMOS" -to RXD[10]
set_instance_assignment -name IO_STANDARD "3.3-V LVCMOS" -to RXD[9]
set_instance_assignment -name IO_STANDARD "3.3-V LVCMOS" -to RXD[8]
set_instance_assignment -name IO_STANDARD "3.3-V LVCMOS" -to RXD[7]
set_instance_assignment -name IO_STANDARD "3.3-V LVCMOS" -to RXD[6]
set_instance_assignment -name IO_STANDARD "3.3-V LVCMOS" -to RXD[5]
set_instance_assignment -name IO_STANDARD "3.3-V LVCMOS" -to RXD[4]
set_instance_assignment -name IO_STANDARD "3.3-V LVCMOS" -to RXD[3]
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
set_instance_assignment -name IO_STANDARD "3.3-V LVCMOS" -to FX3_FPGA_SNN
set_instance_assignment -name IO_STANDARD "3.3-V LVCMOS" -to RPI_GPIO19
set_instance_assignment -name IO_STANDARD "3.3-V LVCMOS" -to RPI_GPIO26
set_instance_assignment -name IO_STANDARD "3.3-V LVCMOS" -to RPI_GPIO6
set_instance_assignment -name IO_STANDARD "3.3-V LVCMOS" -to RPI_GPIO13
set_instance_assignment -name IO_STANDARD "3.3-V LVCMOS" -to FX3_GPIO5
set_instance_assignment -name IO_STANDARD "3.3-V LVCMOS" -to RPI_MISO
set_instance_assignment -name IO_STANDARD "3.3-V LVCMOS" -to RPI_MOSI
set_instance_assignment -name IO_STANDARD "3.3-V LVCMOS" -to RPI_SCLK
set_instance_assignment -name IO_STANDARD "3.3-V LVCMOS" -to RPI_SDA1
set_instance_assignment -name IO_STANDARD "3.3-V LVCMOS" -to RPI_GEN0
set_instance_assignment -name IO_STANDARD "3.3-V LVCMOS" -to RPI_GCLK
set_instance_assignment -name IO_STANDARD "3.3-V LVCMOS" -to RPI_GEN3
set_instance_assignment -name IO_STANDARD "3.3-V LVCMOS" -to RPI_GEN4
set_instance_assignment -name IO_STANDARD "3.3-V LVCMOS" -to RPI_ID_SD
set_location_assignment PIN_C2 -to MCLK2
set_instance_assignment -name IO_STANDARD "3.3-V LVCMOS" -to MCLK2
set_location_assignment PIN_D2 -to FCLK2
set_instance_assignment -name IO_STANDARD "3.3-V LVCMOS" -to FCLK2
set_location_assignment PIN_N1 -to MCLK1
set_location_assignment PIN_K2 -to FCLK1
set_instance_assignment -name IO_STANDARD "3.3-V LVCMOS" -to MCLK1
set_instance_assignment -name IO_STANDARD "3.3-V LVCMOS" -to FCLK1
set_location_assignment PIN_D6 -to unused_pin
set_instance_assignment -name IO_STANDARD "3.3-V LVCMOS" -to unused_pin
set_instance_assignment -name WEAK_PULL_UP_RESISTOR ON -to unused_pin
set_global_assignment -name SDC_FILE SDC1.sdc
set_global_assignment -name VHDL_FILE src/PhCorr/iqbal18.vhd
set_global_assignment -name VHDL_FILE src/GCorr/gcorr18.vhd
set_global_assignment -name VHDL_FILE src/DCCorr/dccorra.vhd
set_global_assignment -name QIP_FILE ip/clkctrl/clkctrl/synthesis/clkctrl.qip
set_global_assignment -name QIP_FILE ip/ddr2/ddr2.qip
set_global_assignment -name QIP_FILE ip/pll2/pll2.qip
set_global_assignment -name QIP_FILE ip/ddrox1/ddrox1.qip
set_global_assignment -name QIP_FILE ip/trxdfifo/trxdfifo.qip
set_global_assignment -name QIP_FILE ip/fifo_16to32/fifo_16to32.qip
set_global_assignment -name QIP_FILE ip/fifo_32to16/fifo_32to16.qip
set_global_assignment -name QIP_FILE ip/pll_reconfig_module/pll_reconfig_module.qip
set_global_assignment -name QIP_FILE ip/iobuff/iobuff.qip
set_global_assignment -name SIGNALTAP_FILE signal_tap/pll_phase.stp
set_global_assignment -name SIGNALTAP_FILE signal_tap/phy_clk.stp
set_global_assignment -name VHDL_FILE src/general/debounce.vhd
set_global_assignment -name VHDL_FILE src/general/alive.vhd
set_global_assignment -name VHDL_FILE src/general/iqmux12.vhd
set_global_assignment -name VHDL_FILE src/dyn_ps/pll_ps_cntrl.vhd
set_global_assignment -name VHDL_FILE src/pll_reconfig_ctrl/config_ctrl.vhd
set_global_assignment -name VHDL_FILE src/spi/miso_mux.vhd
set_global_assignment -name VHDL_FILE src/spi/txtspcfg.vhd
set_global_assignment -name VHDL_FILE src/spi/mem_package.vhd
set_global_assignment -name VHDL_FILE src/spi/mcfg32wm_fsm.vhd
set_global_assignment -name VHDL_FILE src/spi/mcfg_components.vhd
set_global_assignment -name VHDL_FILE src/ram/data_gen.vhd
set_global_assignment -name VHDL_FILE src/ram/rfifo_ctrl.vhd
set_global_assignment -name VHDL_FILE src/ram/fifo_read.vhd
set_global_assignment -name VHDL_FILE src/ram/ram_control.vhd
set_global_assignment -name VHDL_FILE src/fifo/sl_ctrl.vhd
set_global_assignment -name VHDL_FILE src/nco/nco_bin_sin.vhd
set_global_assignment -name VHDL_FILE src/FX3/slaveFIFO2b_streamOUT.vhd
set_global_assignment -name VHDL_FILE src/FX3/slaveFIFO2b_streamINOUT.vhd
set_global_assignment -name VHDL_FILE src/FX3/slaveFIFO2b_streamIN.vhd
set_global_assignment -name VHDL_FILE src/general/iqrxdemux12.vhd
set_global_assignment -name CDF_FILE output_files/Chain1.cdf
set_global_assignment -name BDF_FILE lms7_uStream_trx_top.bdf
set_global_assignment -name SEARCH_PATH ip/ -tag from_archive
set_global_assignment -name SEARCH_PATH src/ -tag from_archive
set_instance_assignment -name PARTITION_HIERARCHY root_partition -to | -section_id Top
