myriadrf/STREAM/stream_openrisc_soc/quartus/src/stream/ip/ddr2_ctrl/ddr2_ctrl_phy_alt_mem_phy.v

//

`default_nettype none

`ifdef ALT_MEM_PHY_DEFINES
`else
`include "alt_mem_phy_defines.v"
`endif

//
(* altera_attribute = "-name MESSAGE_DISABLE 14130" *) module ddr2_ctrl_phy_alt_mem_phy (
                        //Clock and reset inputs:
                        pll_ref_clk,
                        global_reset_n,
                        soft_reset_n,

                        // Used to indicate PLL loss of lock for system reset management:
                        reset_request_n,

                        // Clock and reset for the controller interface:
                        ctl_clk,
                        ctl_reset_n,

                        // Write data interface:
                        ctl_dqs_burst,
                        ctl_wdata_valid,
                        ctl_wdata,
                        ctl_dm,
                        ctl_wlat,

                        // Address and command interface:
                        ctl_addr,
                        ctl_ba,
                        ctl_cas_n,
                        ctl_cke,
                        ctl_cs_n,
                        ctl_odt,
                        ctl_ras_n,
                        ctl_we_n,
                        ctl_rst_n,
                        ctl_mem_clk_disable,

                        // Read data interface:
                        ctl_doing_rd,
                        ctl_rdata,
                        ctl_rdata_valid,
                        ctl_rlat,

                        //re-calibration request & configuration:
                        ctl_cal_req,
                        ctl_cal_byte_lane_sel_n,

                        //Calibration status interface:
                        ctl_cal_success,
                        ctl_cal_fail,
                        ctl_cal_warning,

                        //ports to memory device(s):
                        mem_addr,
                        mem_ba,
                        mem_cas_n,
                        mem_cke,
                        mem_cs_n,
                        mem_dm,
                        mem_odt,
                        mem_ras_n,
                        mem_we_n,
                        mem_clk,
                        mem_clk_n,
                        mem_reset_n,

                        // Bidirectional Memory interface signals:
                        mem_dq,
                        mem_dqs,
                        mem_dqs_n,

                        // Auxiliary clocks. Some systems may need these for debugging
                        // purposes, or for full-rate to half-rate bridge interfaces
                        aux_half_rate_clk,
                        aux_full_rate_clk,

                        // Debug interface:- ALTERA USE ONLY
                        dbg_clk,
                        dbg_reset_n,
                        dbg_addr,
                        dbg_wr,
                        dbg_rd,
                        dbg_cs,
                        dbg_wr_data,
                        dbg_rd_data,
                        dbg_waitrequest

                      );


// Default parameter values :

parameter FAMILY                          =     "CYCLONEIII";
parameter MEM_IF_MEMTYPE                  =           "DDR2";
parameter LEVELLING                       =                0; // RFU
parameter SPEED_GRADE                     =             "C6";
parameter DLL_DELAY_BUFFER_MODE           =           "HIGH";
parameter DLL_DELAY_CHAIN_LENGTH          =                8;
parameter DQS_DELAY_CTL_WIDTH             =                6;
parameter DQS_OUT_MODE                    =   "DELAY_CHAIN2";
parameter DQS_PHASE                       =             9000;
parameter DQS_PHASE_SETTING               =                2;
parameter DWIDTH_RATIO                    =                4;
parameter MEM_IF_DWIDTH                   =               64;
parameter MEM_IF_ADDR_WIDTH               =               13;
parameter MEM_IF_BANKADDR_WIDTH           =                3;
parameter MEM_IF_CS_WIDTH                 =                2;
parameter MEM_IF_DM_WIDTH                 =                8;
parameter MEM_IF_DM_PINS_EN               =                1;
parameter MEM_IF_DQ_PER_DQS               =                8;
parameter MEM_IF_DQS_WIDTH                =                8;
parameter MEM_IF_OCT_EN                   =                0;
parameter MEM_IF_CLK_PAIR_COUNT           =                3;
parameter MEM_IF_CLK_PS                   =             4000;
parameter MEM_IF_CLK_PS_STR               =        "4000 ps";
parameter MEM_IF_MR_0                     =                0;
parameter MEM_IF_MR_1                     =                0;
parameter MEM_IF_MR_2                     =                0;
parameter MEM_IF_MR_3                     =                0;
parameter MEM_IF_PRESET_RLAT              =                0;
parameter PLL_STEPS_PER_CYCLE             =               24;
parameter SCAN_CLK_DIVIDE_BY              =                4;
parameter REDUCE_SIM_TIME                 =                0;
parameter CAPABILITIES                    =                0;
parameter TINIT_TCK                       =            40000;
parameter TINIT_RST                       =           100000;
parameter DBG_A_WIDTH                     =               13;
parameter SEQ_STRING_ID                   =       "seq_name";
parameter MEM_IF_CS_PER_RANK              =                1;    // duplicates CS, CKE, ODT, sequencer still controls 1 rank, but it is subdivided from controller perspective.
parameter MEM_IF_RANKS_PER_SLOT           =                1;    // how ranks are arranged into slot - needed for odt setting in the sequencer
parameter MEM_IF_RDV_PER_CHIP             =                0;   // multiple chips, and which gives valid data
parameter GENERATE_ADDITIONAL_DBG_RTL     =                0;   // DDR2 sequencer specific
parameter CAPTURE_PHASE_OFFSET            =                0;
parameter MEM_IF_ADDR_CMD_PHASE           =                0;
parameter DLL_EXPORT_IMPORT               =           "NONE";
parameter MEM_IF_DQSN_EN                  =                1;

parameter RANK_HAS_ADDR_SWAP              =                0;

//
localparam phy_report_prefix              = "ddr2_ctrl_phy_alt_mem_phy (top level) : ";
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
